TomRolander/LEGO_DNA_Sequencer/Arduino Code/Unit Test/LEGO_DNA_Sequencer_TCS34725/LEGO_DNA_Sequencer_TCS34725.ino

/**************************************************************************
  LEGO DNA Sequencer
  TCS34725 Color Sensor Unit Test
  
  Original Code:  2022-12-24

  Tom Rolander, MSEE
  Mentor for Circuit Design, Software, 3D Printing
  Miller Library, Fabrication Lab
  Hopkins Marine Station, Stanford University,
  120 Ocean View Blvd, Pacific Grove, CA 93950
  +1 831.915.9526 | rolander@stanford.edu

 **************************************************************************/

#define PROGRAM "LEGO DNA Sequencer - TCS34725 Color Sensor Unit Test"
#define VERSION "Ver 0.2 2025-08-04"

#define DEBUG_OUTPUT 1

#include <Wire.h>
#include "Adafruit_TCS34725.h"

#define CLEAR   -1
#define RED     3
#define GREEN   2
#define BLUE    1
#define YELLOW  0

#define LED_TCS34725  A3

#define FLORA 1

#if FLORA
#define CLEAR_CHANNEL_THRESHHOLD  3149
#define RED_CHANNEL_THRESHHOLD  700
#define BLUE_CHANNEL_THRESHHOLD  823
#else
#define CLEAR_CHANNEL_THRESHHOLD  900
#define RED_CHANNEL_THRESHHOLD  170
#define BLUE_CHANNEL_THRESHHOLD  220
#endif

static int iCLEAR_CHANNEL_THRESHHOLD = CLEAR_CHANNEL_THRESHHOLD;
static int iRED_CHANNEL_THRESHHOLD = RED_CHANNEL_THRESHHOLD;
static int iBLUE_CHANNEL_THRESHHOLD = BLUE_CHANNEL_THRESHHOLD;

/* Initialise with specific int time and gain values */
Adafruit_TCS34725 tcs = Adafruit_TCS34725(TCS34725_INTEGRATIONTIME_50MS, TCS34725_GAIN_16X);

void setup(void) {
  Serial.begin(115200);
  delay(1000);
  Serial.println();
  Serial.println(PROGRAM);
  Serial.println(VERSION);
  Serial.println("");

  Serial.println("Remove LEGO tray");
  Serial.println("Remove the gear from the top of the stepper motor shaft");
  Serial.println("Insert the 10 LEGO test bricks YYRRBBGGYY into the LEGO tray");
  Serial.println("Manually slide the LEGO tray backwards and forwards under the sensor");
  delay(5000);


  pinMode (LED_TCS34725, OUTPUT); 
  digitalWrite (LED_TCS34725, LOW); 
  if (tcs.begin()) {
    Serial.println("Found sensor");
    // LED off to prevent overheating
    tcs.setInterrupt(true);
  } else {
    Serial.println("No TCS34725 found ... check your connections");
    while (1);
  }

  Serial.println("Delay 5 seconds, then turn on LED light");
  delay(5000);
  digitalWrite (LED_TCS34725, HIGH); 
  tcs.setInterrupt(false);
}

void print4digits(int iVal)
{
  if (iVal < 10) {
    Serial.print("   "); // 3 spaces
  } else if (iVal < 100) {
    Serial.print("  "); // 2 spaces
  } else if (iVal < 1000) {
    Serial.print(" "); // 1 space
  } 
  Serial.print(iVal);
}

void loop(void) {
  uint16_t r, g, b, c;
  tcs.getRawData(&r, &g, &b, &c);
  Serial.print("Red: "); print4digits(r); Serial.print(" ");
  Serial.print("Green: "); print4digits(g); Serial.print(" ");
  Serial.print("Blue: "); print4digits(b); Serial.print(" ");
  Serial.print("Clear: "); print4digits(c); Serial.print(" ");  
  Serial.print(F("DNA: "));  

  if (c >= iCLEAR_CHANNEL_THRESHHOLD)
  {
    Serial.print("C"); Serial.print(" ");  
    Serial.println(F("YELLOW"));
  }
  else if (r >= iRED_CHANNEL_THRESHHOLD)
  {
    Serial.print("G"); Serial.print(" ");  
    Serial.println(F("RED"));
 }
  else if (b >= iBLUE_CHANNEL_THRESHHOLD)
  {
    Serial.print("T"); Serial.print(" ");  
    Serial.println(F("BLUE"));
  }
  else
    /* if (g > b && g > r) */
  {
    Serial.print("A"); Serial.print(" ");  
    Serial.println(F("GREEN"));
  }
  
  delay(1000);
}
