TomRolander/LEGO_DNA_Sequencer/Arduino Code/Unit Test/LEGO_DNA_Sequencer_LCD_And_Rotary_Encoder/LEGO_DNA_Sequencer_LCD_And_Rotary_Encoder.ino

/**************************************************************************
  LEGO DNA Sequencer
  LCD and Button Unit Test
  
  Original Code:  2022-12-24

  Tom Rolander, MSEE
  Mentor for Circuit Design, Software, 3D Printing
  Miller Library, Fabrication Lab
  Hopkins Marine Station, Stanford University,
  120 Ocean View Blvd, Pacific Grove, CA 93950
  +1 831.915.9526 | rolander@stanford.edu

 **************************************************************************/

#define PROGRAM "LEGO DNA Sequencer - LCD and Rotary Encoder Unit Test"
#define VERSION "Ver 0.1 2023-04-19"

#define DEBUG_OUTPUT 1

#define LED_TCS34725  A3

#include <LiquidCrystal.h>
int Contrast = 75;
LiquidCrystal lcd(8, 7, 5, 4, 3, 2);

// Rotary Encoder Inputs
#define CLK A1
#define DT A2
#define SW 13

int counter = 0;
int currentStateCLK;
int lastStateCLK;
String currentDir ="";
unsigned long lastButtonPress = 0;

void setup()
{
  Serial.begin(115200);
  delay(1000);
  Serial.println();
  Serial.println(PROGRAM);
  Serial.println(VERSION);

  // Set encoder pins as inputs
  pinMode(CLK,INPUT);
  pinMode(DT,INPUT);
  pinMode(SW, INPUT_PULLUP);

  // Read the initial state of CLK
  lastStateCLK = digitalRead(CLK);

  //pinMode(13, INPUT_PULLUP);
  
  analogWrite(6, Contrast);
  lcd.begin(16, 2);

  pinMode (LED_TCS34725, OUTPUT); 
  digitalWrite (LED_TCS34725, LOW); 

  lcd.setCursor(0, 0);
//lcd.print("          1     ");
//lcd.print("0123456789012345");
  lcd.print("LCD Unit Testing");
  
  lcd.setCursor(0, 1);
  lcd.print(" Rotary Encoder ");

  delay(2000);
  
  lcd.setCursor(0, 0);
  lcd.print(" Rotary Encoder ");
  lcd.setCursor(0, 1);
  lcd.print("                ");
}
void loop()
{
  // Read the current state of CLK
  currentStateCLK = digitalRead(CLK);

  // If last and current state of CLK are different, then pulse occurred
  // React to only 1 state change to avoid double count
  if (currentStateCLK != lastStateCLK  && currentStateCLK == 1){

    // If the DT state is different than the CLK state then
    // the encoder is rotating CCW so decrement
    if (digitalRead(DT) != currentStateCLK) {
      counter --;
      currentDir ="CCW";
    } else {
      // Encoder is rotating CW so increment
      counter ++;
      currentDir ="CW";
    }

    Serial.print("Direction: ");
    Serial.print(currentDir);
    Serial.print(" | Counter: ");
    Serial.println(counter);

    lcd.setCursor(0, 1);
    lcd.print("                ");
    lcd.setCursor(0, 1);
    lcd.print("Counter = ");
    lcd.print(counter);    
  }

  // Remember last CLK state
  lastStateCLK = currentStateCLK;

  // Read the button state
  int btnState = digitalRead(SW);

  //If we detect LOW signal, button is pressed
  if (btnState == LOW) {
    //if 50ms have passed since last LOW pulse, it means that the
    //button has been pressed, released and pressed again
    if (millis() - lastButtonPress > 50) {
      Serial.println("Button pressed!");
      lcd.setCursor(0, 1);
      lcd.print("Button pressed! ");
    }

    // Remember last button press event
    lastButtonPress = millis();
  }

  // Put in a slight delay to help debounce the reading
  delay(1);
}
